JanClyde05/Danger-Monitor-System/Transmitter/pcb/Screenshot 2026-02-09 194333.png

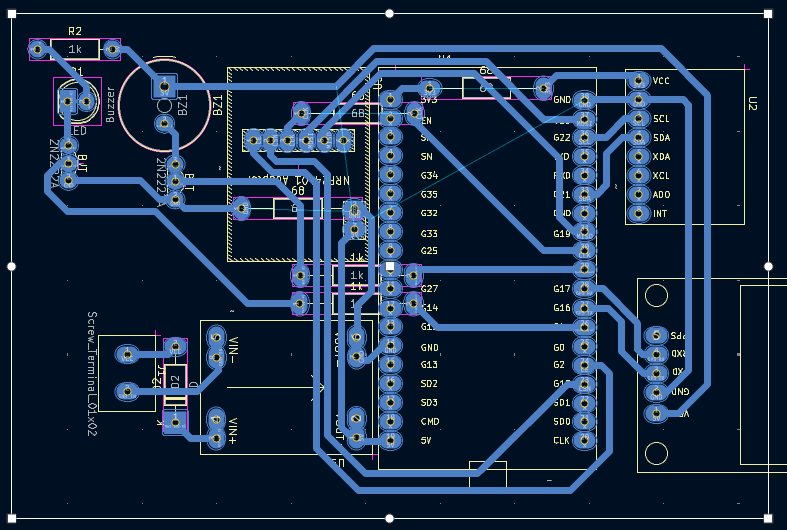
Transmitter/pcb/Screenshot 2026-02-09 194333.png
