JanClyde05/Danger-Monitor-System/web profile/Picture DB/jl.jpg

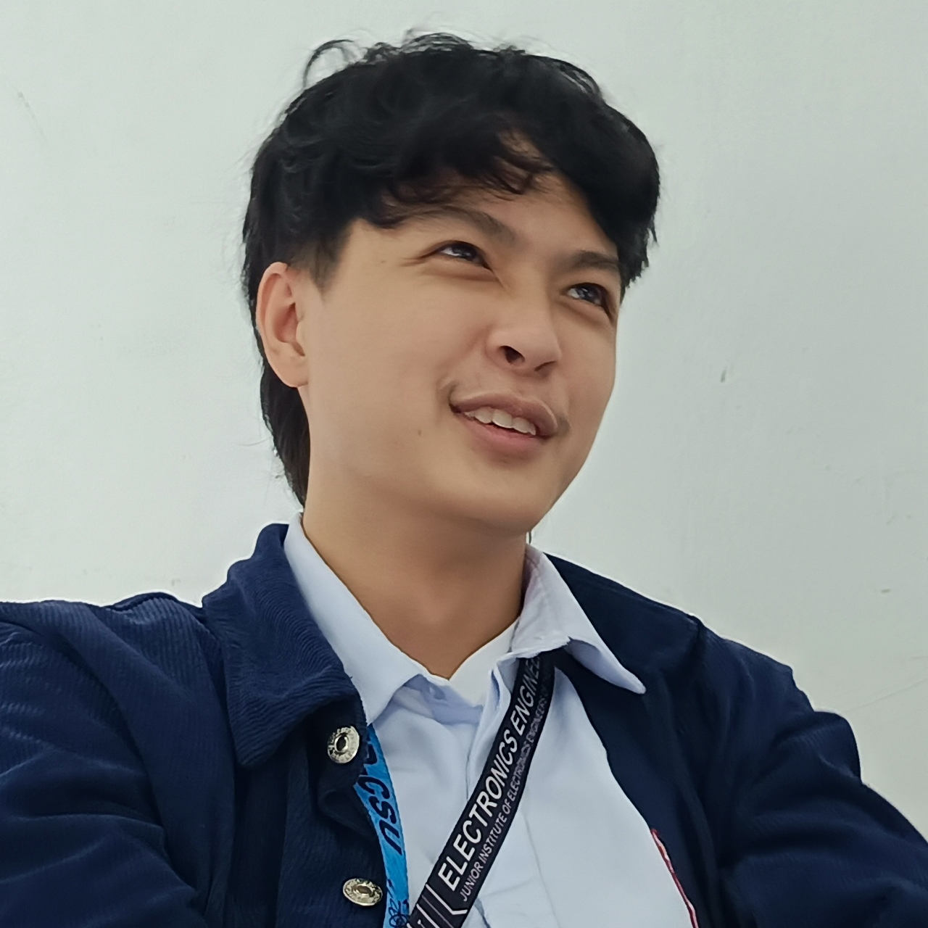
web profile/Picture DB/jl.jpg
