JanClyde05/Danger-Monitor-System/web profile/Picture DB/kaye.jpeg

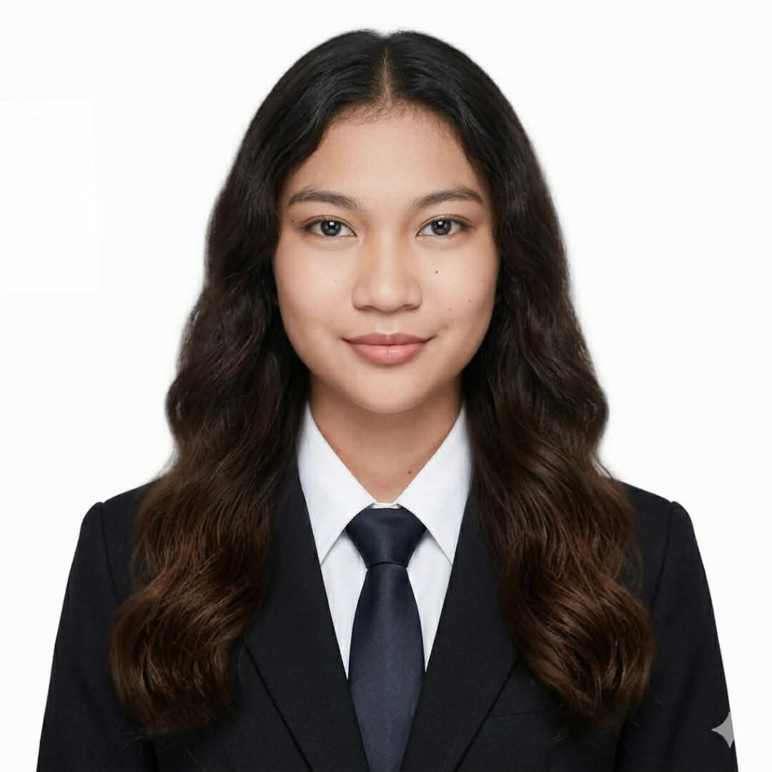
web profile/Picture DB/kaye.jpeg
