JanClyde05/Danger-Monitor-System/web profile/Picture DB/rina.jpg

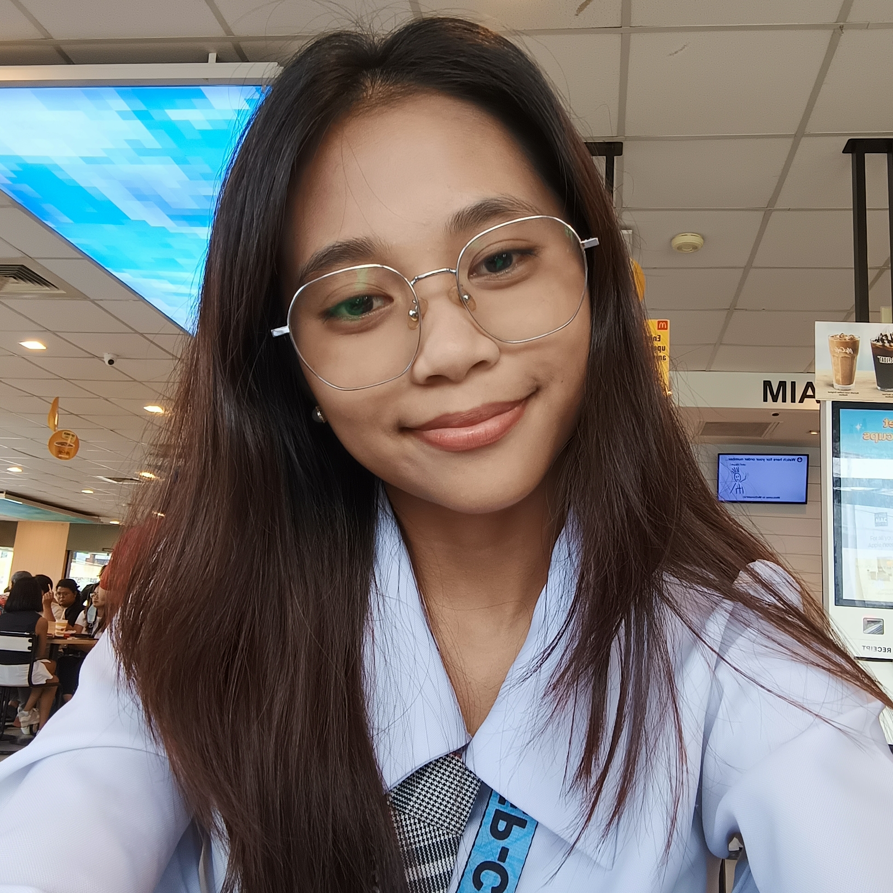
web profile/Picture DB/rina.jpg
