JanClyde05/Danger-Monitor-System/web profile/Picture DB/sham.jpeg

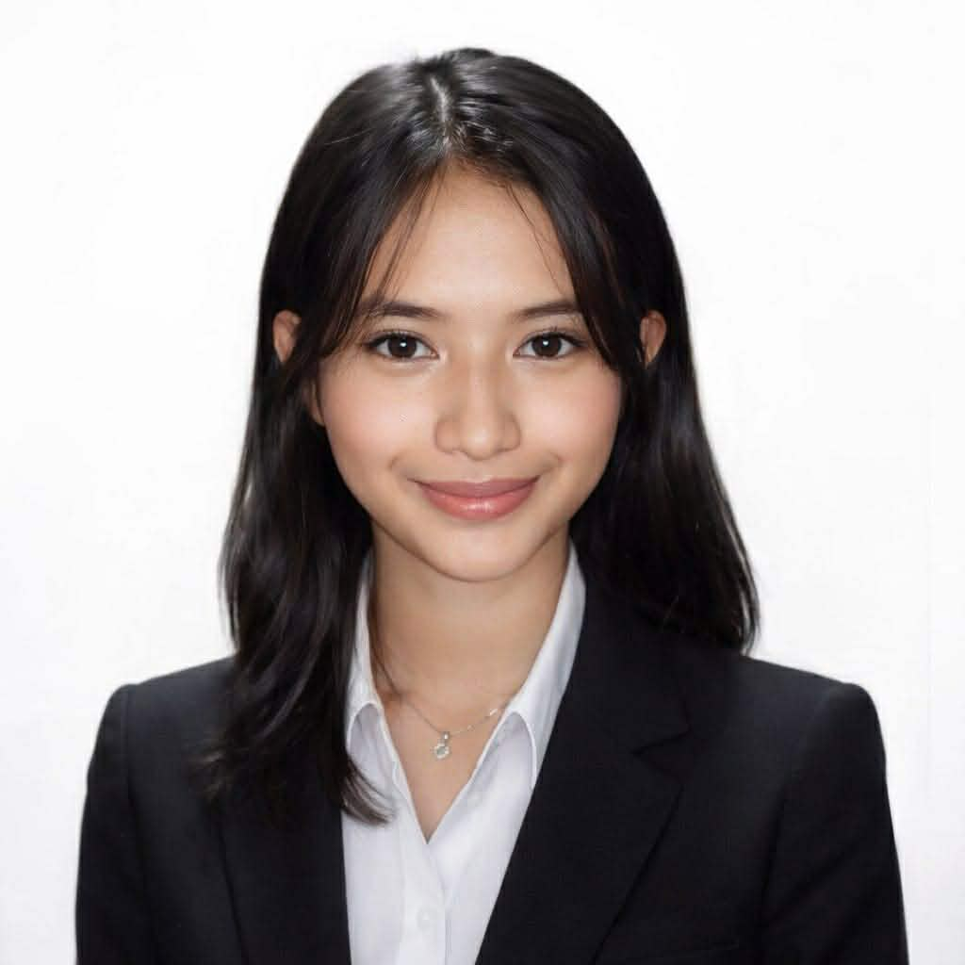
web profile/Picture DB/sham.jpeg
